AnotherBuildCorner/Hyper_Wheel/Images/RevA1 PCB Pricing.png

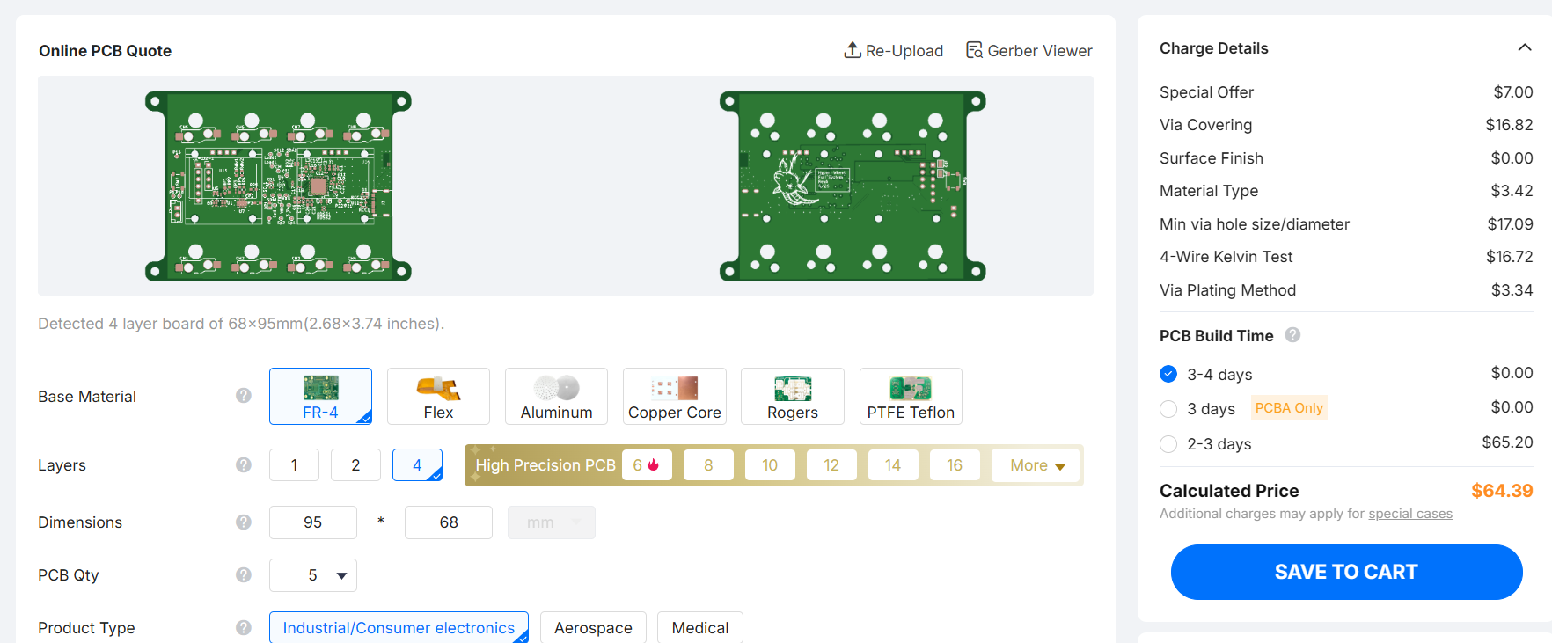
Images/RevA1 PCB Pricing.png
