AnotherBuildCorner/Hyper_Wheel/Ref/Screenshot 2026-04-17 091756.png

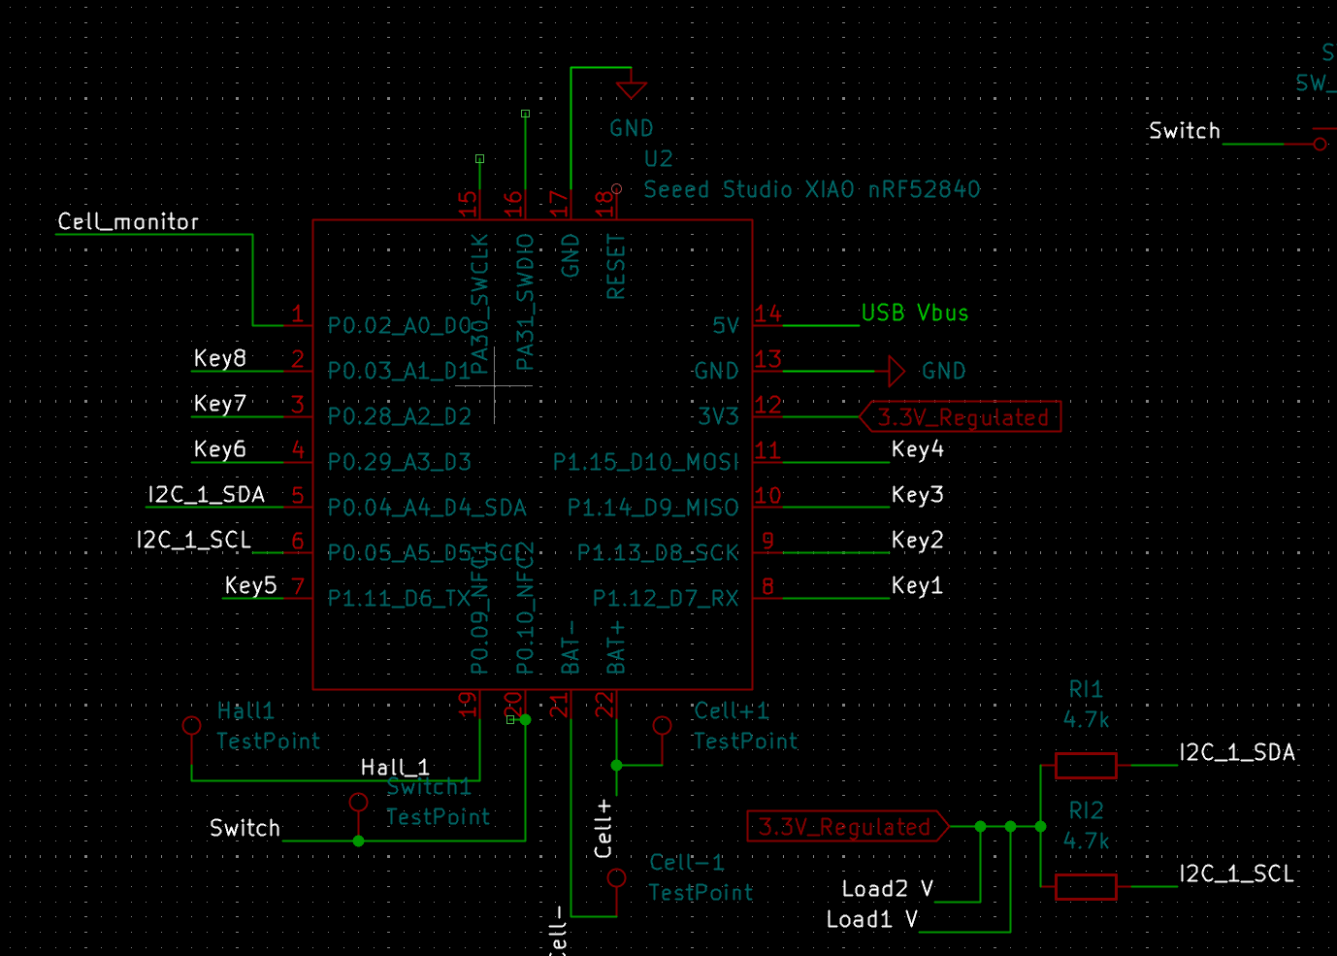
Ref/Screenshot 2026-04-17 091756.png
