AnotherBuildCorner/Hyper_Wheel/PCB/Hyper_Wheel_XIAO/Vendor Parts/marbastlib-main/marbastlib-main/resources/repolist.png

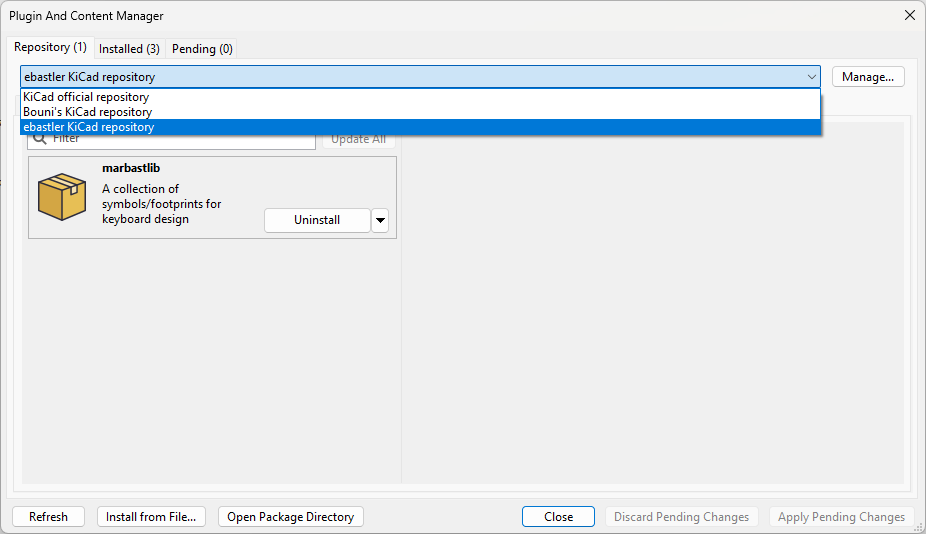
PCB/Hyper_Wheel_XIAO/Vendor Parts/marbastlib-main/marbastlib-main/resources/repolist.png
