AnotherBuildCorner/Hyper_Wheel/PCB/Hyper_Wheel_XIAO/Vendor Parts/marbastlib-main/marbastlib-main/3dmodels/CON_781710004.step

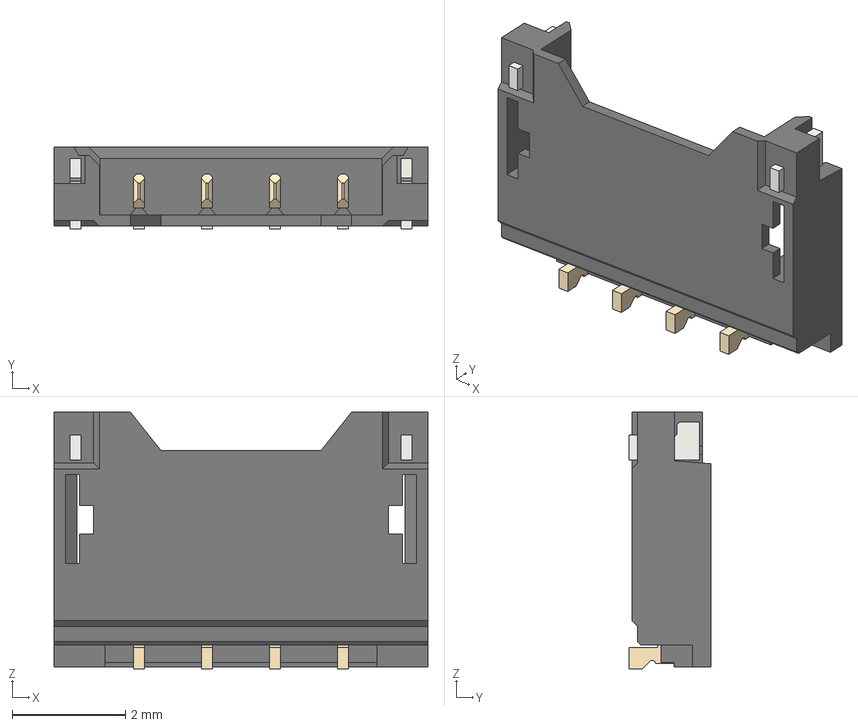
[picture p37: CAD file, 2026-04-03]
PCB/Hyper_Wheel_XIAO/Vendor Parts/marbastlib-main/marbastlib-main/3dmodels/CON_781710004.step
6.60 x 1.45 x 4.53 mm
