AnotherBuildCorner/Hyper_Wheel/PCB/Hyper_Wheel_XIAO/Vendor Parts/marbastlib-main/marbastlib-main/3dmodels/Texas_X2QFN-12_1.6x1.6mm.step

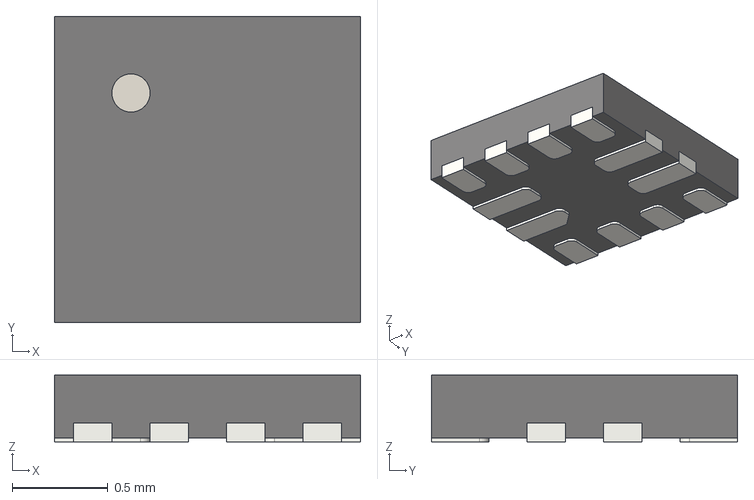
[picture p38: CAD file, 2026-04-03]
PCB/Hyper_Wheel_XIAO/Vendor Parts/marbastlib-main/marbastlib-main/3dmodels/Texas_X2QFN-12_1.6x1.6mm.step
1.60 x 1.60 x 0.35 mm
