AnotherBuildCorner/Hyper_Wheel/PCB/Hyper_Wheel_XIAO/Vendor Parts/marbastlib-main/marbastlib-main/3dmodels/CON_SM13B-SRSS-TB.step

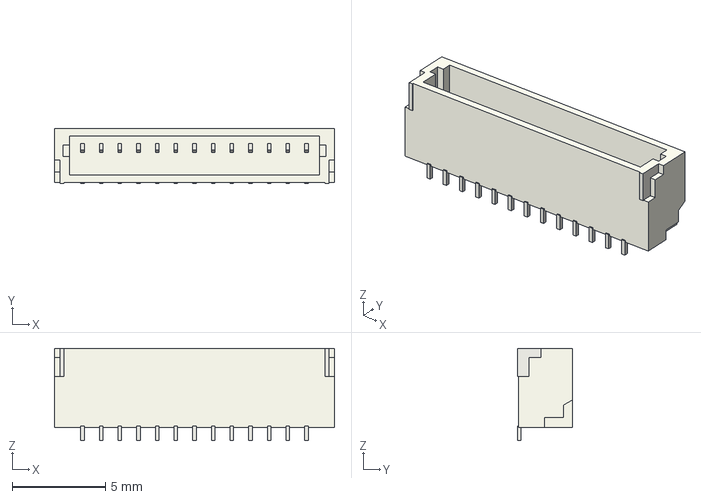
[picture p39: CAD file, 2026-04-03]
PCB/Hyper_Wheel_XIAO/Vendor Parts/marbastlib-main/marbastlib-main/3dmodels/CON_SM13B-SRSS-TB.step
15.0 x 2.96 x 4.95 mm
