AnotherBuildCorner/Hyper_Wheel/PCB/Hyper_Wheel_XIAO/Vendor Parts/marbastlib-main/marbastlib-main/3dmodels/ebyte_E73-2G4M08S1C.step

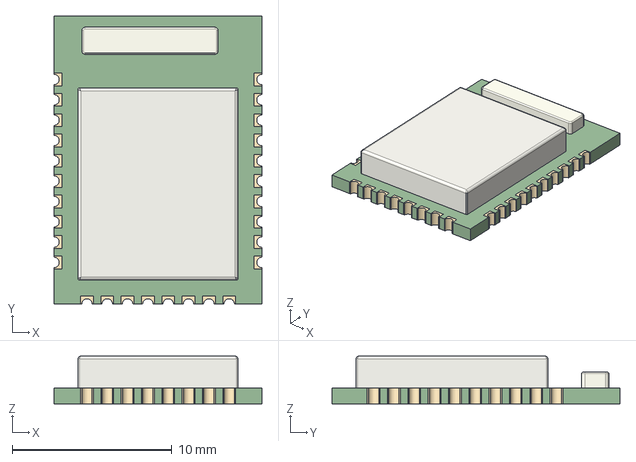
[picture p41: CAD file, 2026-04-03]
PCB/Hyper_Wheel_XIAO/Vendor Parts/marbastlib-main/marbastlib-main/3dmodels/ebyte_E73-2G4M08S1C.step
13.0 x 18.0 x 3.00 mm
