AnotherBuildCorner/Hyper_Wheel/PCB/Hyper_Wheel_XIAO/Vendor Parts/marbastlib-main/marbastlib-main/3dmodels/SpringContact_SameSky_CPG-45-TH-TR.step

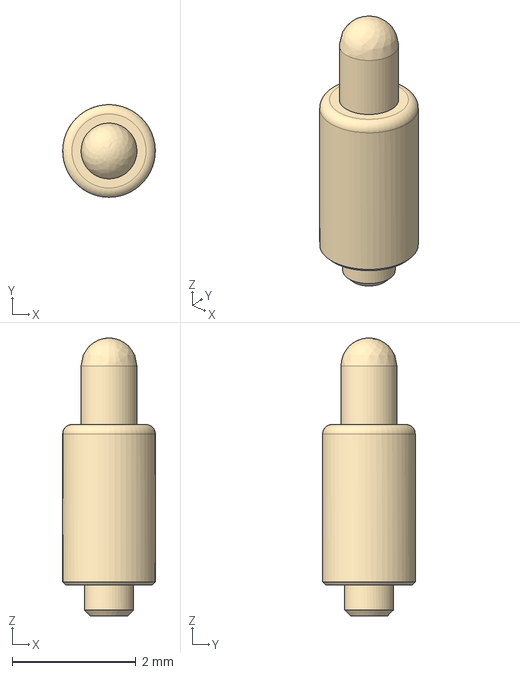
[picture p42: CAD file, 2026-04-03]
PCB/Hyper_Wheel_XIAO/Vendor Parts/marbastlib-main/marbastlib-main/3dmodels/SpringContact_SameSky_CPG-45-TH-TR.step
1.50 x 1.50 x 4.50 mm
