AnotherBuildCorner/Hyper_Wheel/PCB/Hyper_Wheel_XIAO/Vendor Parts/marbastlib-main/marbastlib-main/3dmodels/HS_CPG151101S11_MX.step

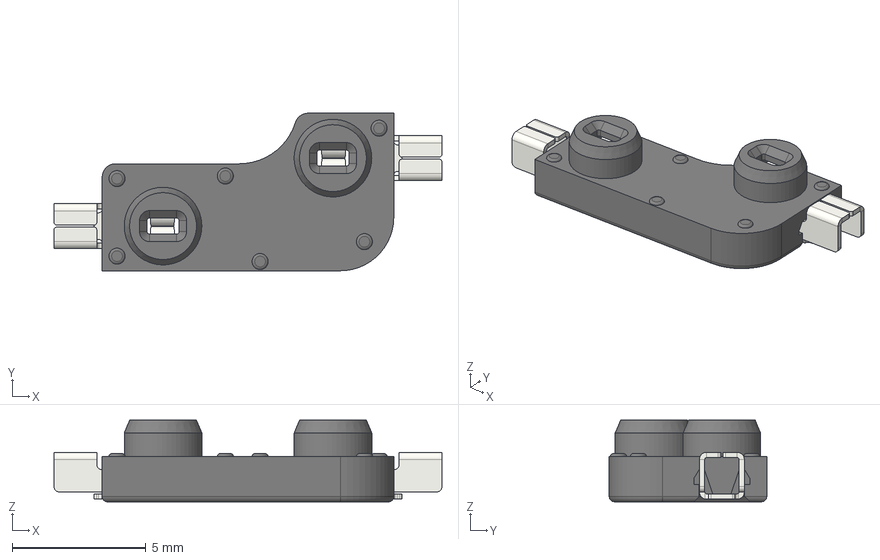
[picture p43: CAD file, 2026-04-03]
PCB/Hyper_Wheel_XIAO/Vendor Parts/marbastlib-main/marbastlib-main/3dmodels/HS_CPG151101S11_MX.step
14.5 x 5.89 x 3.05 mm
Contact x 2
