AnotherBuildCorner/Hyper_Wheel/PCB/Hyper_Wheel_XIAO/Vendor Parts/marbastlib-main/marbastlib-main/3dmodels/SW_SPDT_Alps_SSAJ110100.step

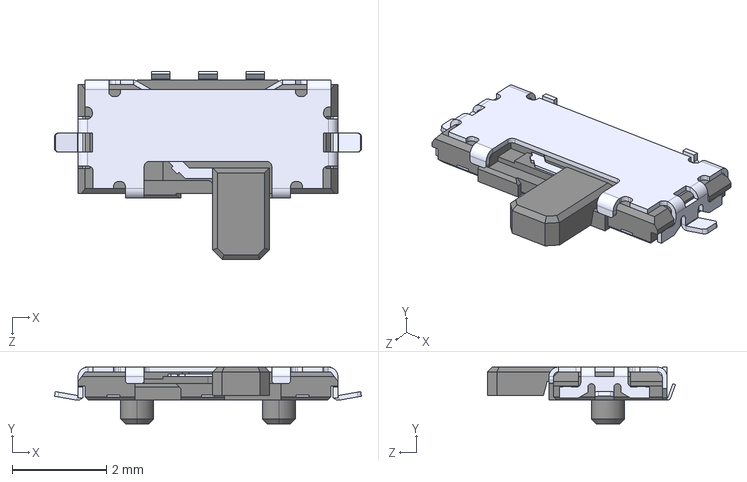
[picture p44: CAD file, 2026-04-03]
PCB/Hyper_Wheel_XIAO/Vendor Parts/marbastlib-main/marbastlib-main/3dmodels/SW_SPDT_Alps_SSAJ110100.step
6.50 x 1.20 x 3.98 mm
