AnotherBuildCorner/Hyper_Wheel/PCB/Hyper_Wheel_XIAO/Vendor Parts/marbastlib-main/marbastlib-main/3dmodels/HS_KS-2P02B01-02_KS33.step

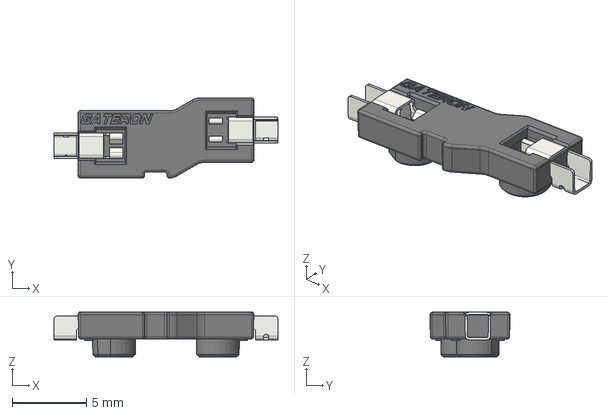
[picture p48: CAD file, 2026-04-03]
PCB/Hyper_Wheel_XIAO/Vendor Parts/marbastlib-main/marbastlib-main/3dmodels/HS_KS-2P02B01-02_KS33.step
15.1 x 5.39 x 3.00 mm
