AnotherBuildCorner/Hyper_Wheel/PCB/Hyper_Wheel_XIAO/Vendor Parts/marbastlib-main/marbastlib-main/3dmodels/SW_Kailh_ULP_CPG1316M_CAP.step

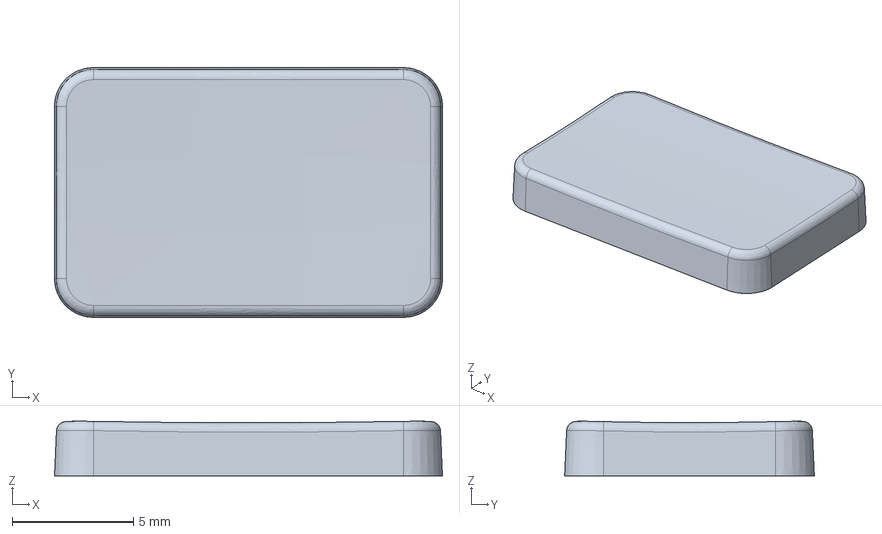
[picture p49: CAD file, 2026-04-03]
PCB/Hyper_Wheel_XIAO/Vendor Parts/marbastlib-main/marbastlib-main/3dmodels/SW_Kailh_ULP_CPG1316M_CAP.step
16.0 x 10.3 x 2.25 mm
