AnotherBuildCorner/Hyper_Wheel/PCB/Hyper_Wheel_XIAO/Vendor Parts/marbastlib-main/marbastlib-main/3dmodels/QFN-14_2x2_Pitch0.4mm.step

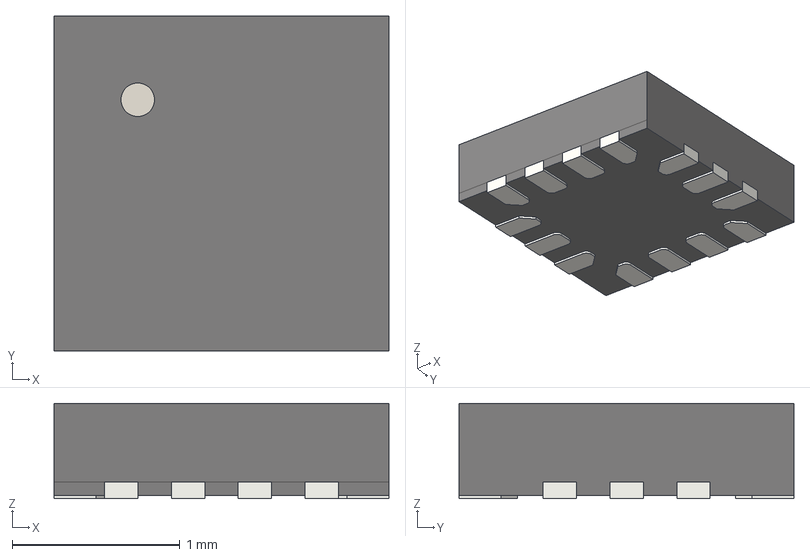
[picture p50: CAD file, 2026-04-03]
PCB/Hyper_Wheel_XIAO/Vendor Parts/marbastlib-main/marbastlib-main/3dmodels/QFN-14_2x2_Pitch0.4mm.step
2.00 x 2.00 x 0.57 mm
