AnotherBuildCorner/Hyper_Wheel/PCB/Hyper_Wheel_XIAO/Vendor Parts/marbastlib-main/marbastlib-main/3dmodels/SW_Kailh_ULP_CPG1316M.step

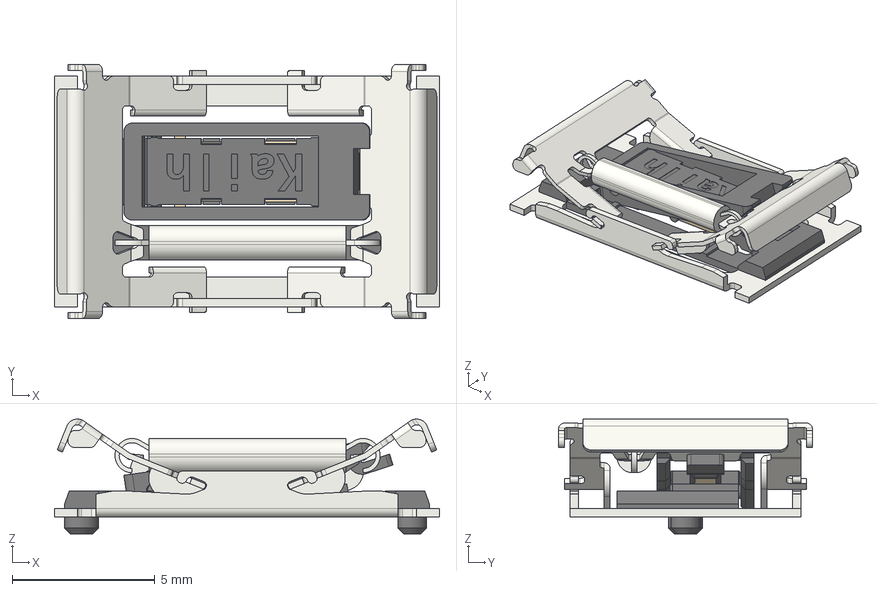
[picture p52: CAD file, 2026-04-03]
PCB/Hyper_Wheel_XIAO/Vendor Parts/marbastlib-main/marbastlib-main/3dmodels/SW_Kailh_ULP_CPG1316M.step
13.5 x 8.90 x 4.03 mm
1316S-»ù×ù¿¨¼þ
PG1316S-»ù×ù
Çý¶¯¸Ë
Æ½ºâ¼Ü-B¼þ
À»É
PG1316S-¶¯½Ó´¥Æ¬-´ ø´¥µã
PG1316S-¾²Æ¬-´ø´¥µ ã
Æ½ºâ¼Ü
