AnotherBuildCorner/Hyper_Wheel/PCB/Hyper_Wheel_XIAO/Vendor Parts/marbastlib-main/marbastlib-main/3dmodels/CON_TYPE-C-31-M-14.step

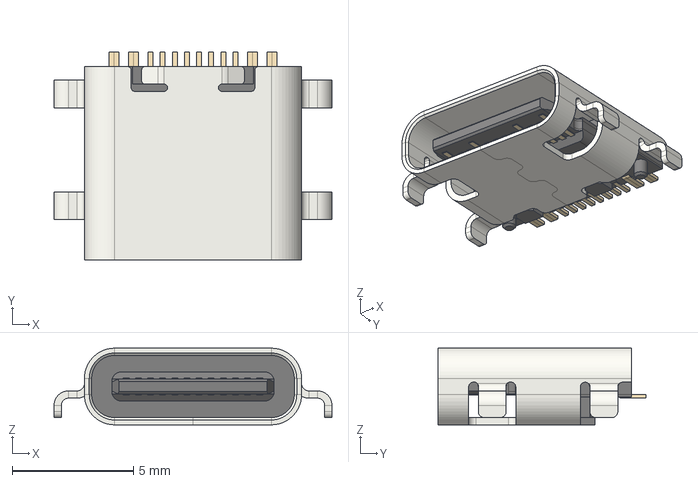
[picture p55: CAD file, 2026-04-03]
PCB/Hyper_Wheel_XIAO/Vendor Parts/marbastlib-main/marbastlib-main/3dmodels/CON_TYPE-C-31-M-14.step
11.5 x 8.56 x 3.16 mm
Shroud
Plastic Body & Connector
