AnotherBuildCorner/Hyper_Wheel/PCB/Hyper_Wheel_XIAO/Vendor Parts/marbastlib-main/marbastlib-main/3dmodels/CON_HC-PBB40C-10DS-0.4V-2.0-02.step

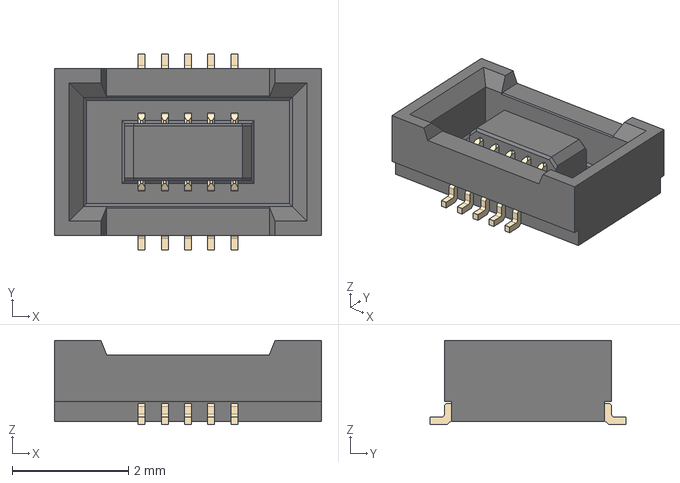
[picture p56: CAD file, 2026-04-03]
PCB/Hyper_Wheel_XIAO/Vendor Parts/marbastlib-main/marbastlib-main/3dmodels/CON_HC-PBB40C-10DS-0.4V-2.0-02.step
4.60 x 3.38 x 1.45 mm
