AnotherBuildCorner/Hyper_Wheel/PCB/Hyper_Wheel_XIAO/Vendor Parts/marbastlib-main/marbastlib-main/3dmodels/Crystal_SMD_2016-4Pin_2.0x1.6mm.step

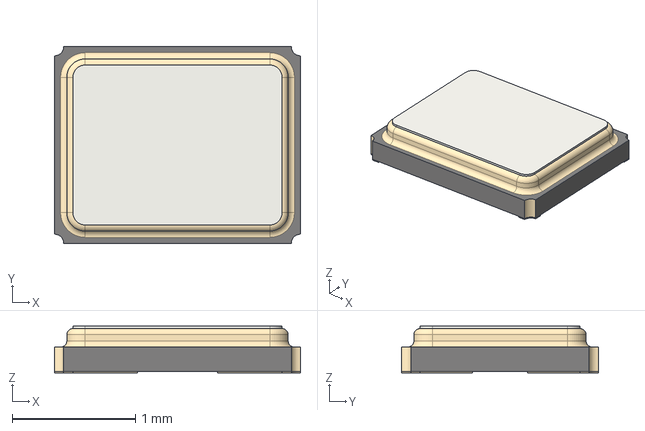
[picture p65: CAD file, 2026-04-03]
PCB/Hyper_Wheel_XIAO/Vendor Parts/marbastlib-main/marbastlib-main/3dmodels/Crystal_SMD_2016-4Pin_2.0x1.6mm.step
2.00 x 1.60 x 0.38 mm
