AnotherBuildCorner/Hyper_Wheel/PCB/Hyper_Wheel_XIAO/Vendor Parts/marbastlib-main/marbastlib-main/3dmodels/CON_XUNPU_FPC-0.5AL-20PB.step

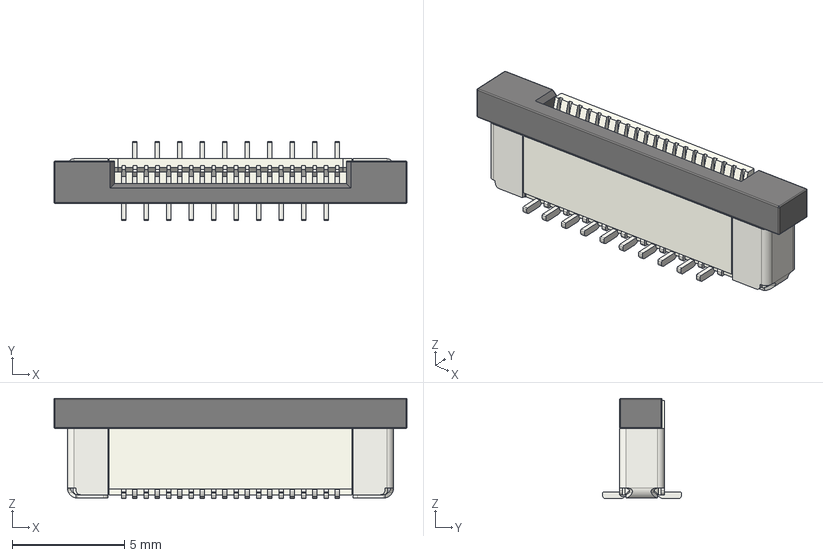
[picture p66: CAD file, 2026-04-03]
PCB/Hyper_Wheel_XIAO/Vendor Parts/marbastlib-main/marbastlib-main/3dmodels/CON_XUNPU_FPC-0.5AL-20PB.step
15.7 x 3.52 x 4.47 mm
