AnotherBuildCorner/Hyper_Wheel/PCB/Hyper_Wheel_XIAO/Vendor Parts/marbastlib-main/marbastlib-main/3dmodels/RP2040-Matrix.step

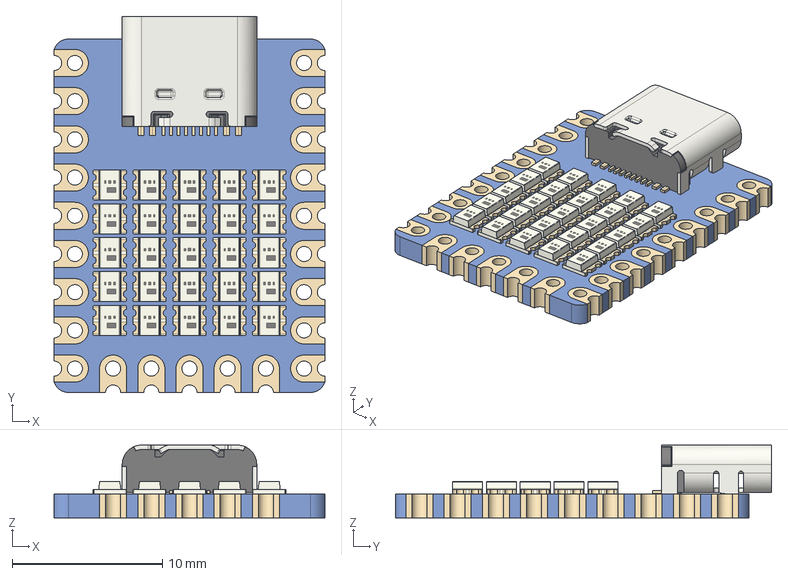
[picture p69: CAD file, 2026-04-03]
PCB/Hyper_Wheel_XIAO/Vendor Parts/marbastlib-main/marbastlib-main/3dmodels/RP2040-Matrix.step
18.0 x 25.0 x 4.85 mm
LED_WS2812_2020 x 25
ConPins
PcbPins
Mold
Frame
