AnotherBuildCorner/Hyper_Wheel/PCB/Hyper_Wheel_XIAO/Vendor Parts/marbastlib-main/marbastlib-main/3dmodels/ROT_SKYLOONG_HS.step

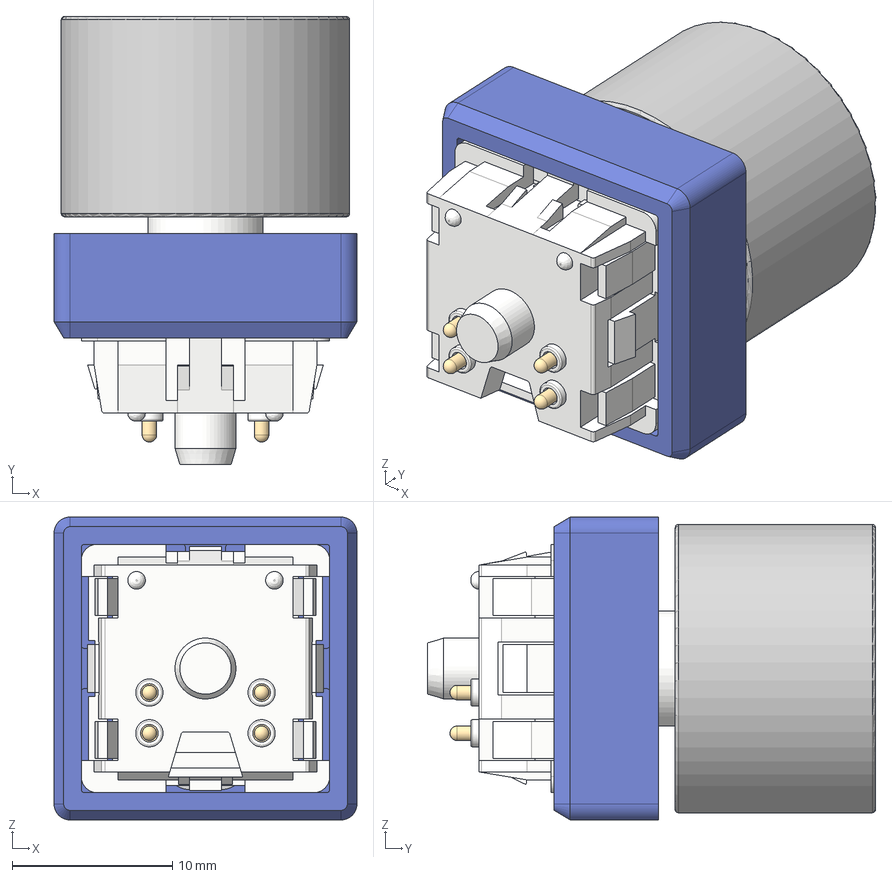
[picture p72: CAD file, 2026-04-03]
PCB/Hyper_Wheel_XIAO/Vendor Parts/marbastlib-main/marbastlib-main/3dmodels/ROT_SKYLOONG_HS.step
18.9 x 27.9 x 18.9 mm
Top
Shaft
Pogo Pin x 4
Bottom
Top_1
Cover
Knob
