AnotherBuildCorner/Hyper_Wheel/PCB/Hyper_Wheel_XIAO/Vendor Parts/marbastlib-main/marbastlib-main/3dmodels/ANT_Johanson_2450AT18D0100001E v1.step

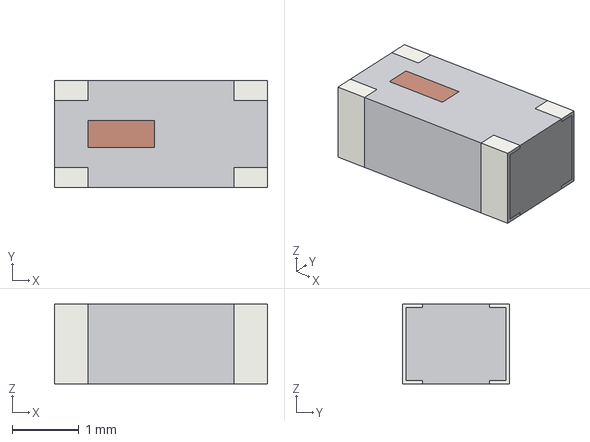
[picture p75: CAD file, 2026-04-03]
PCB/Hyper_Wheel_XIAO/Vendor Parts/marbastlib-main/marbastlib-main/3dmodels/ANT_Johanson_2450AT18D0100001E v1.step
3.20 x 1.60 x 1.20 mm
