AnotherBuildCorner/Hyper_Wheel/PCB/Hyper_Wheel_XIAO/Vendor Parts/marbastlib-main/marbastlib-main/3dmodels/L_Bourns_SRP6050CA.step

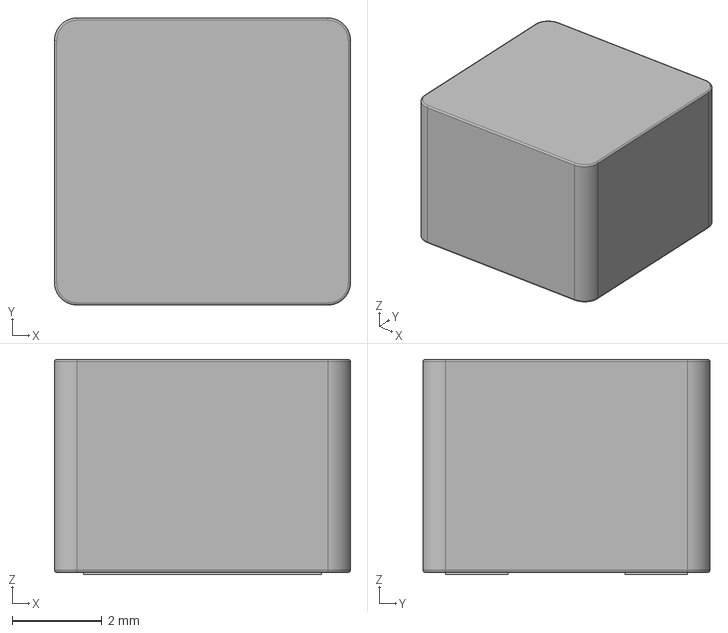
[picture p76: CAD file, 2026-04-03]
PCB/Hyper_Wheel_XIAO/Vendor Parts/marbastlib-main/marbastlib-main/3dmodels/L_Bourns_SRP6050CA.step
6.60 x 6.40 x 4.80 mm
