AnotherBuildCorner/Hyper_Wheel/PCB/Hyper_Wheel_XIAO/Vendor Parts/marbastlib-main/marbastlib-main/3dmodels/Crystal_SMD_2012-2Pin_2.0x1.2mm.step

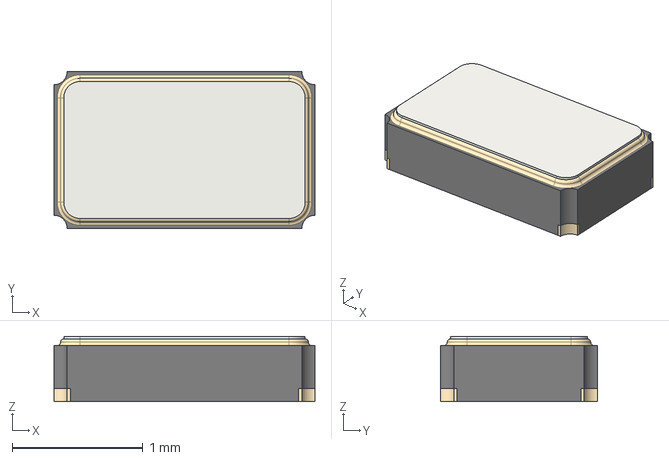
[picture p77: CAD file, 2026-04-03]
PCB/Hyper_Wheel_XIAO/Vendor Parts/marbastlib-main/marbastlib-main/3dmodels/Crystal_SMD_2012-2Pin_2.0x1.2mm.step
2.00 x 1.20 x 0.5 mm
