AnotherBuildCorner/Hyper_Wheel/PCB/Hyper_Wheel_XIAO/Vendor Parts/marbastlib-main/marbastlib-main/3dmodels/CON_XUNPU_FPC-05F-16PH20.step

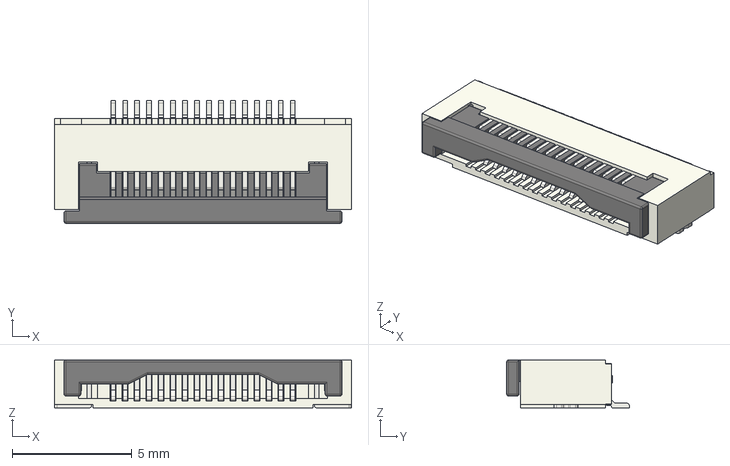
[picture p78: CAD file, 2026-04-03]
PCB/Hyper_Wheel_XIAO/Vendor Parts/marbastlib-main/marbastlib-main/3dmodels/CON_XUNPU_FPC-05F-16PH20.step
12.4 x 5.12 x 2.00 mm
