AnotherBuildCorner/Hyper_Wheel/PCB/Hyper_Wheel_XIAO/Vendor Parts/marbastlib-main/marbastlib-main/3dmodels/USB_C_Receptacle_GCT_USB4510-03-1-A.step

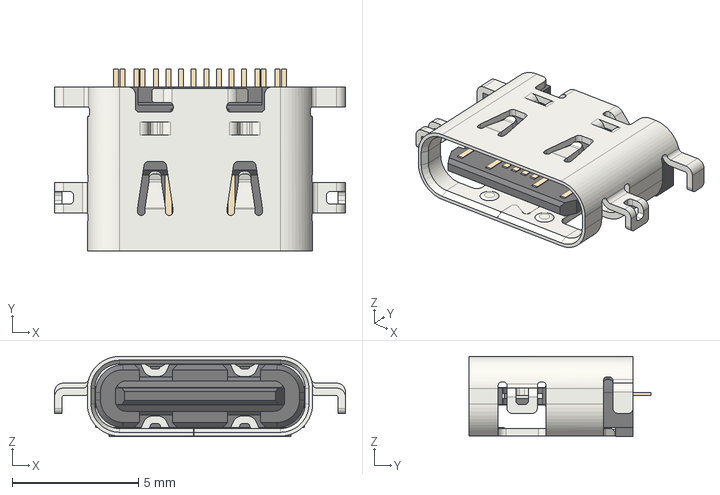
[picture p79: CAD file, 2026-04-03]
PCB/Hyper_Wheel_XIAO/Vendor Parts/marbastlib-main/marbastlib-main/3dmodels/USB_C_Receptacle_GCT_USB4510-03-1-A.step
11.5 x 7.20 x 3.18 mm
