AnotherBuildCorner/Hyper_Wheel/PCB/Hyper_Wheel_XIAO/Vendor Parts/marbastlib-main/marbastlib-main/3dmodels/seeeduino_xiao_rp2040.step

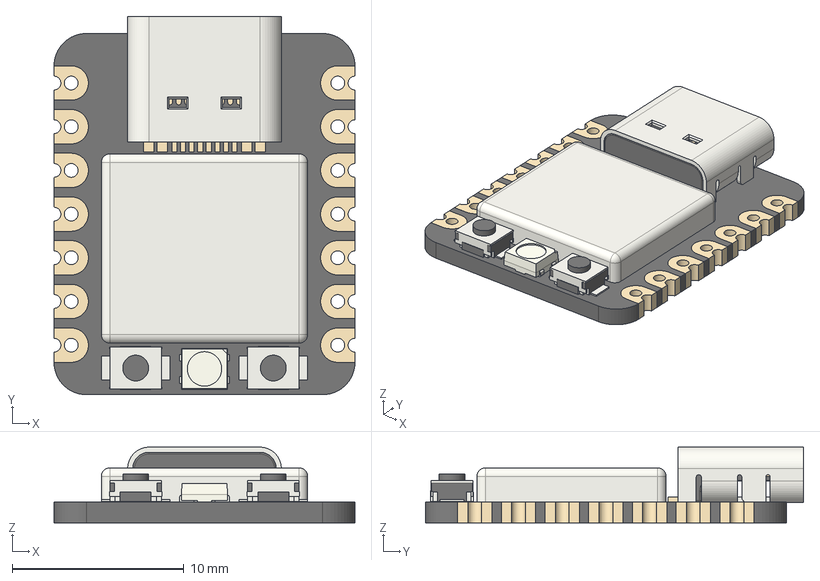
[picture p81: CAD file, 2026-04-03]
PCB/Hyper_Wheel_XIAO/Vendor Parts/marbastlib-main/marbastlib-main/3dmodels/seeeduino_xiao_rp2040.step
17.5 x 22.0 x 4.40 mm
type-c v2
smd_button v3
DOUT
DIN
VSS
VDD
smd_button v3(Mirror)
