AnotherBuildCorner/Hyper_Wheel/PCB/Hyper_Wheel_XIAO/Vendor Parts/marbastlib-main/marbastlib-main/3dmodels/CON_TYPE-C-31-M-12.step

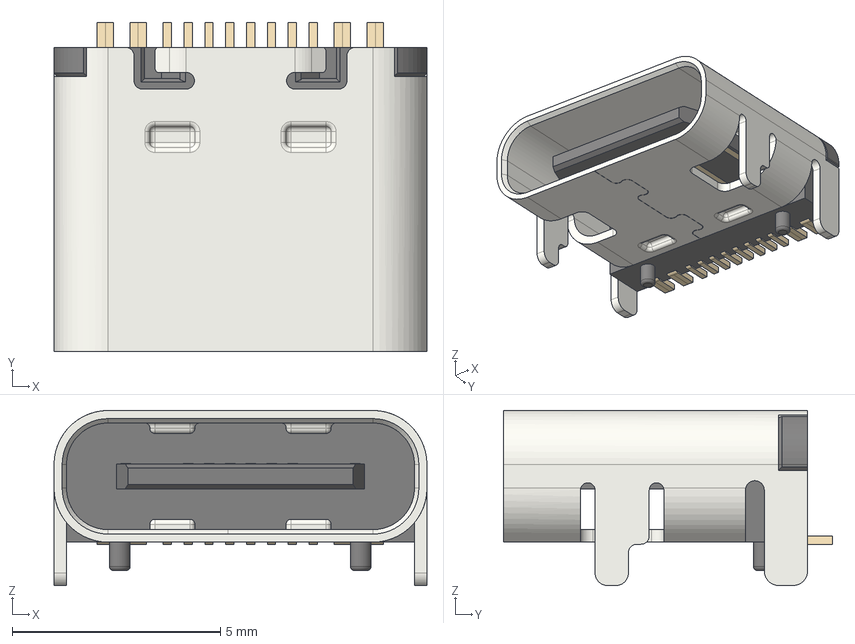
[picture p82: CAD file, 2026-04-03]
PCB/Hyper_Wheel_XIAO/Vendor Parts/marbastlib-main/marbastlib-main/3dmodels/CON_TYPE-C-31-M-12.step
8.95 x 7.90 x 4.20 mm
ConPins
PcbPins
Mold
Frame
