AnotherBuildCorner/Hyper_Wheel/PCB/Hyper_Wheel_XIAO/Vendor Parts/marbastlib-main/marbastlib-main/3dmodels/HS_CPG135001S30_Choc.step

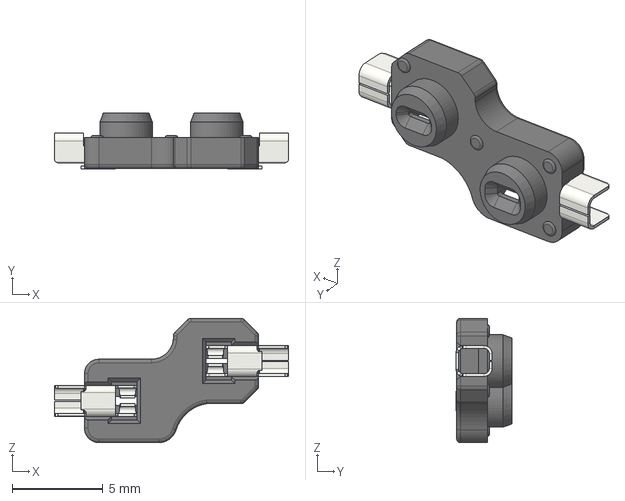
[picture p83: CAD file, 2026-04-03]
PCB/Hyper_Wheel_XIAO/Vendor Parts/marbastlib-main/marbastlib-main/3dmodels/HS_CPG135001S30_Choc.step
12.9 x 3.09 x 6.85 mm
pin x 2
socket
