AnotherBuildCorner/Hyper_Wheel/PCB/Hyper_Wheel_XIAO/Vendor Parts/marbastlib-main/marbastlib-main/3dmodels/SW_Kailh_CPG1316S-2_CAP.step

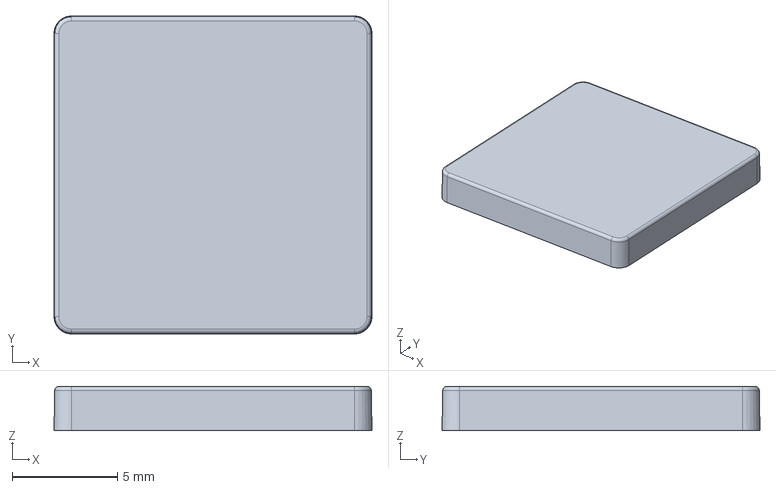
[picture p87: CAD file, 2026-04-03]
PCB/Hyper_Wheel_XIAO/Vendor Parts/marbastlib-main/marbastlib-main/3dmodels/SW_Kailh_CPG1316S-2_CAP.step
15.1 x 15.1 x 2.10 mm
