AnotherBuildCorner/Hyper_Wheel/PCB/Hyper_Wheel_XIAO/Vendor Parts/marbastlib-main/marbastlib-main/3dmodels/Diodes_UDFN1212-3_Type-C.step

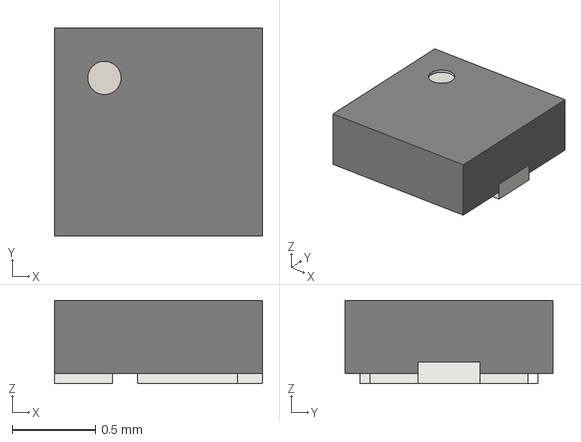
[picture p88: CAD file, 2026-04-03]
PCB/Hyper_Wheel_XIAO/Vendor Parts/marbastlib-main/marbastlib-main/3dmodels/Diodes_UDFN1212-3_Type-C.step
1.25 x 1.25 x 0.5 mm
