AnotherBuildCorner/Hyper_Wheel/PCB/Hyper_Wheel_XIAO/Vendor Parts/marbastlib-main/marbastlib-main/3dmodels/Mounting_Wuerth_WA-SMSI-M2.5_H1mm_9774010151R.step

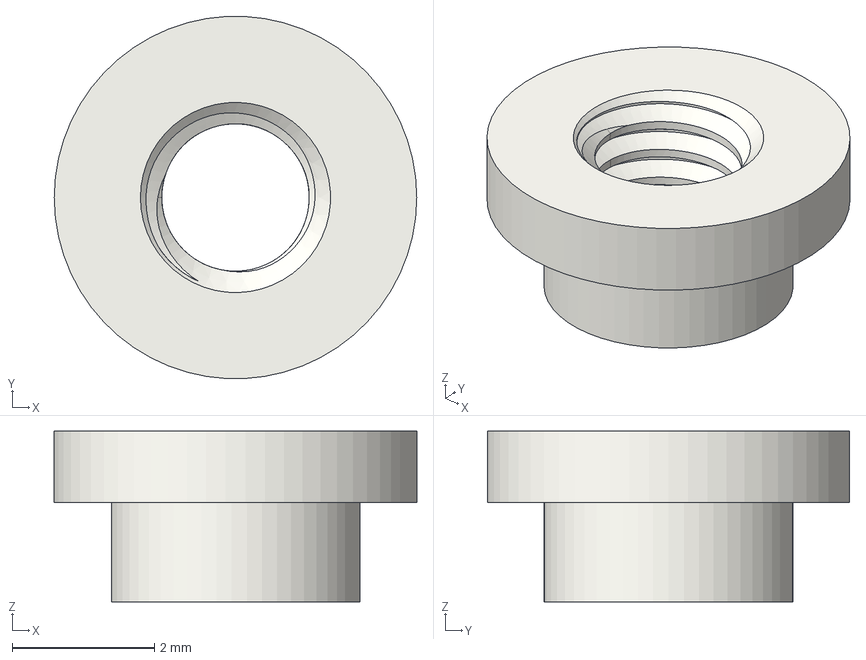
[picture p92: CAD file, 2026-04-03]
PCB/Hyper_Wheel_XIAO/Vendor Parts/marbastlib-main/marbastlib-main/3dmodels/Mounting_Wuerth_WA-SMSI-M2.5_H1mm_9774010151R.step
5.10 x 5.09 x 2.40 mm
