AnotherBuildCorner/Hyper_Wheel/PCB/Hyper_Wheel_XIAO/Vendor Parts/marbastlib-main/marbastlib-main/3dmodels/Speaker_SELTECH_CR1511L025YN8WP.step

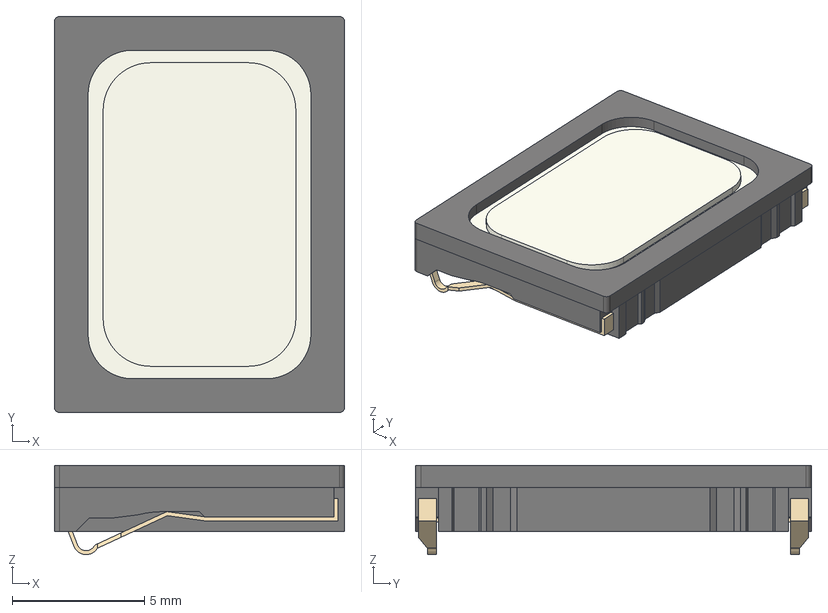
[picture p94: CAD file, 2026-04-03]
PCB/Hyper_Wheel_XIAO/Vendor Parts/marbastlib-main/marbastlib-main/3dmodels/Speaker_SELTECH_CR1511L025YN8WP.step
11.0 x 15.0 x 3.38 mm
