AnotherBuildCorner/Hyper_Wheel/PCB/Hyper_Wheel_XIAO/Vendor Parts/marbastlib-main/marbastlib-main/3dmodels/CON_HytePro_M411P_Receptacle_1x04.step

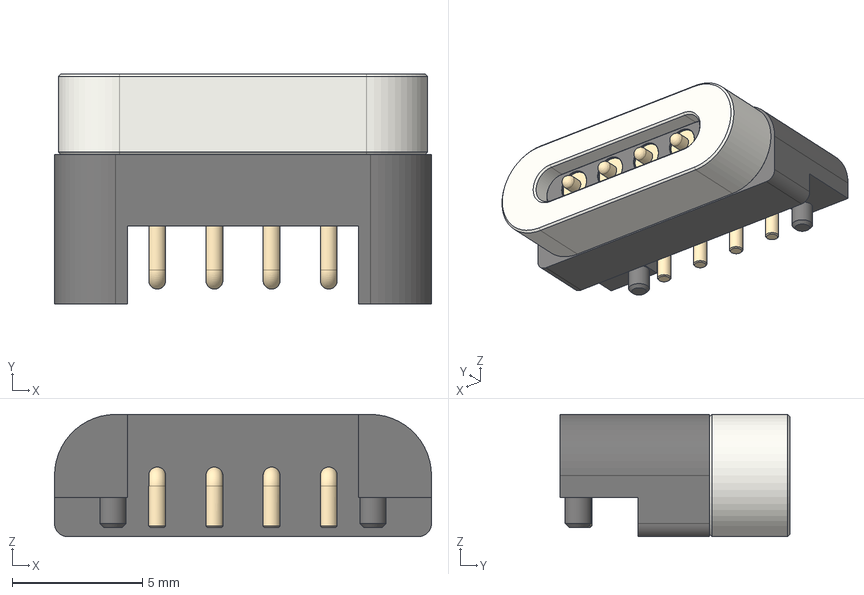
[picture p96: CAD file, 2026-04-03]
PCB/Hyper_Wheel_XIAO/Vendor Parts/marbastlib-main/marbastlib-main/3dmodels/CON_HytePro_M411P_Receptacle_1x04.step
14.5 x 8.85 x 4.70 mm
Magnetic Connector Female - MiddlePart
Magnetic Connector Female-tip_Standard
Magnetic Connector Female v2 - MountingPart
