AnotherBuildCorner/Hyper_Wheel/PCB/Hyper_Wheel_XIAO/Vendor Parts/marbastlib-main/marbastlib-main/3dmodels/Texas_RYK0018A_WQFN-HR-18.step

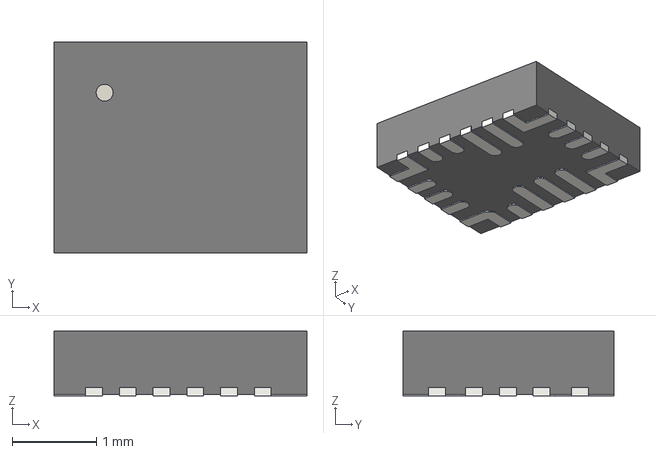
[picture p97: CAD file, 2026-04-03]
PCB/Hyper_Wheel_XIAO/Vendor Parts/marbastlib-main/marbastlib-main/3dmodels/Texas_RYK0018A_WQFN-HR-18.step
3.00 x 2.50 x 0.77 mm
