AnotherBuildCorner/Hyper_Wheel/PCB/Hyper_Wheel_XIAO/Vendor Parts/marbastlib-main/marbastlib-main/3dmodels/CON_HC-PBB40C-10DP-0.4V-02.step

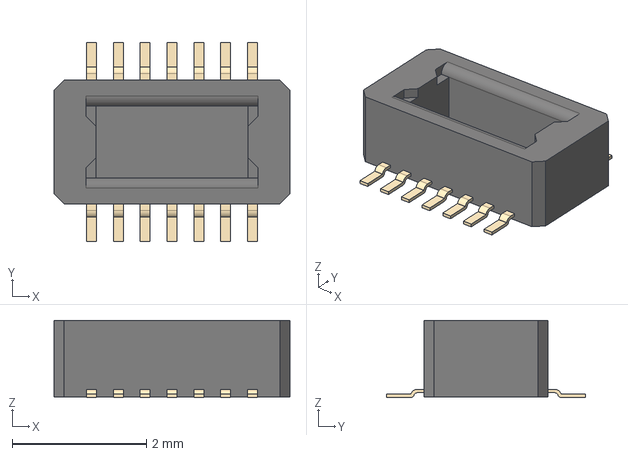
[picture p98: CAD file, 2026-04-03]
PCB/Hyper_Wheel_XIAO/Vendor Parts/marbastlib-main/marbastlib-main/3dmodels/CON_HC-PBB40C-10DP-0.4V-02.step
3.52 x 2.97 x 1.15 mm
