AnotherBuildCorner/Hyper_Wheel/PCB/Hyper_Wheel_XIAO/Vendor Parts/marbastlib-main/marbastlib-main/3dmodels/CON_HytePro_M411P_Plug_1x04.step

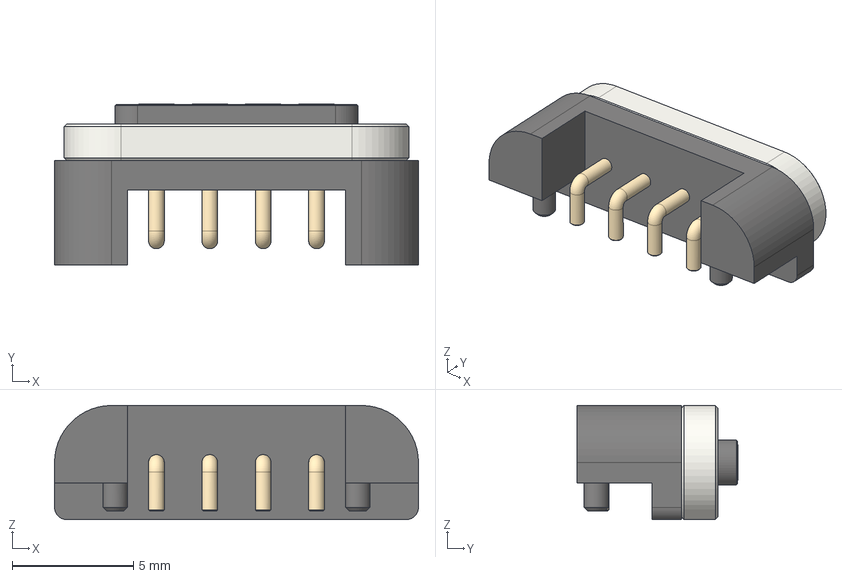
[picture p100: CAD file, 2026-04-03]
PCB/Hyper_Wheel_XIAO/Vendor Parts/marbastlib-main/marbastlib-main/3dmodels/CON_HytePro_M411P_Plug_1x04.step
15.0 x 6.64 x 4.70 mm
Magnetic Connector Male - MiddlePart
Magnetic Connector Male - MountingPart
Magnetic Connector Male-tip_Standard
