AnotherBuildCorner/Hyper_Wheel/PCB/Hyper_Wheel_XIAO/Vendor Parts/marbastlib-main/marbastlib-main/3dmodels/CON_HC-PBB40C-10DS-0.4V-4.0-02.step

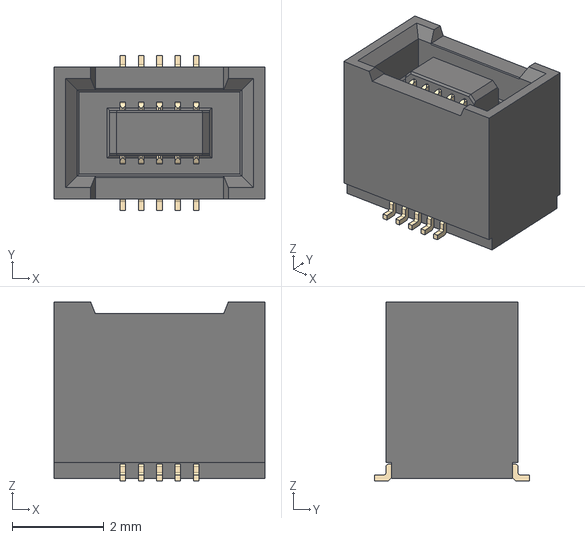
[picture p104: CAD file, 2026-04-03]
PCB/Hyper_Wheel_XIAO/Vendor Parts/marbastlib-main/marbastlib-main/3dmodels/CON_HC-PBB40C-10DS-0.4V-4.0-02.step
4.60 x 3.38 x 3.90 mm
