AnotherBuildCorner/Hyper_Wheel/PCB/Hyper_Wheel_XIAO/Vendor Parts/marbastlib-main/marbastlib-main/3dmodels/Texas_DSBGA-9_1.62x1.58mm_Layout3x3_P0.5mm.step

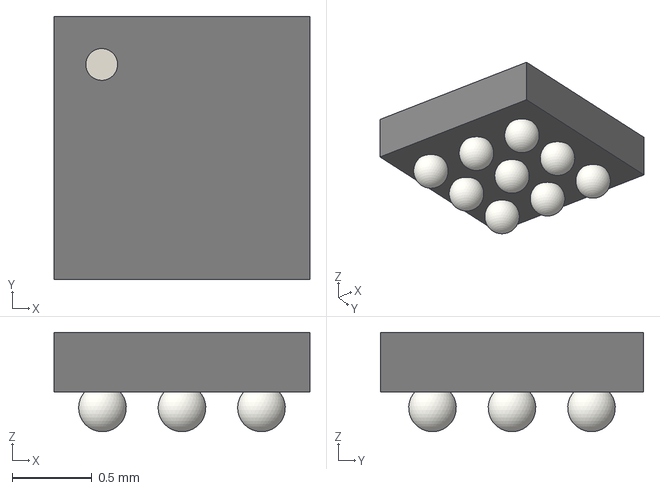
[picture p108: CAD file, 2026-04-03]
PCB/Hyper_Wheel_XIAO/Vendor Parts/marbastlib-main/marbastlib-main/3dmodels/Texas_DSBGA-9_1.62x1.58mm_Layout3x3_P0.5mm.step
1.61 x 1.65 x 0.625 mm
