AnotherBuildCorner/Hyper_Wheel/PCB/Hyper_Wheel_XIAO/Vendor Parts/marbastlib-main/marbastlib-main/3dmodels/USB_C_Receptacle_GCT_USB4505-03-0-A.step

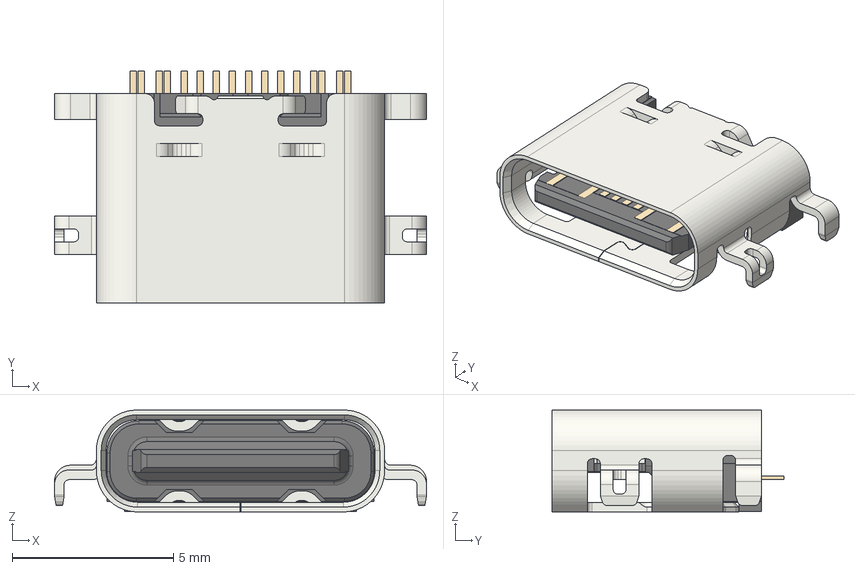
[picture p109: CAD file, 2026-04-03]
PCB/Hyper_Wheel_XIAO/Vendor Parts/marbastlib-main/marbastlib-main/3dmodels/USB_C_Receptacle_GCT_USB4505-03-0-A.step
11.5 x 7.20 x 3.16 mm
USB4505-03-0-A_PART1
USB4505-03-0-A_PART2
