AnotherBuildCorner/Hyper_Wheel/PCB/Hyper_Wheel_XIAO/Vendor Parts/marbastlib-main/marbastlib-main/3dmodels/HS_KS-2P02B01-01_MX.step

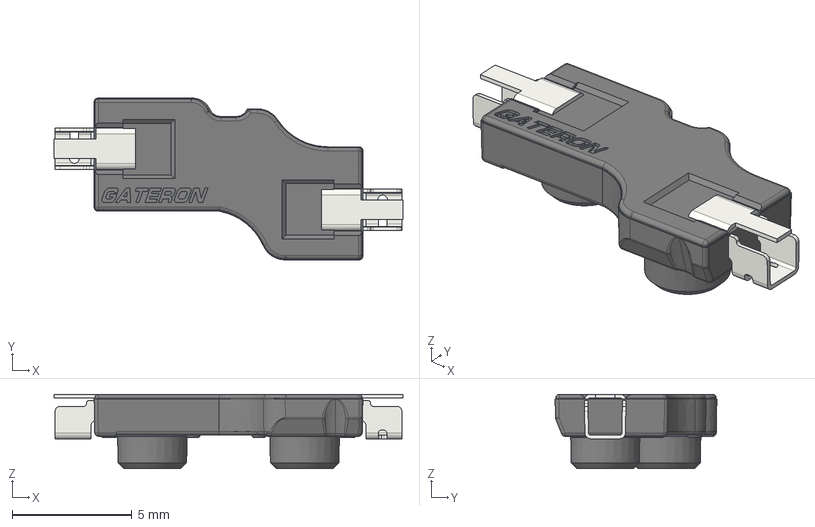
[picture p112: CAD file, 2026-04-03]
PCB/Hyper_Wheel_XIAO/Vendor Parts/marbastlib-main/marbastlib-main/3dmodels/HS_KS-2P02B01-01_MX.step
14.6 x 6.74 x 3.10 mm
