AnotherBuildCorner/Hyper_Wheel/PCB/Hyper_Wheel_XIAO/Vendor Parts/marbastlib-main/marbastlib-main/3dmodels/QFN-13_3x4mm_P0.5mm.step

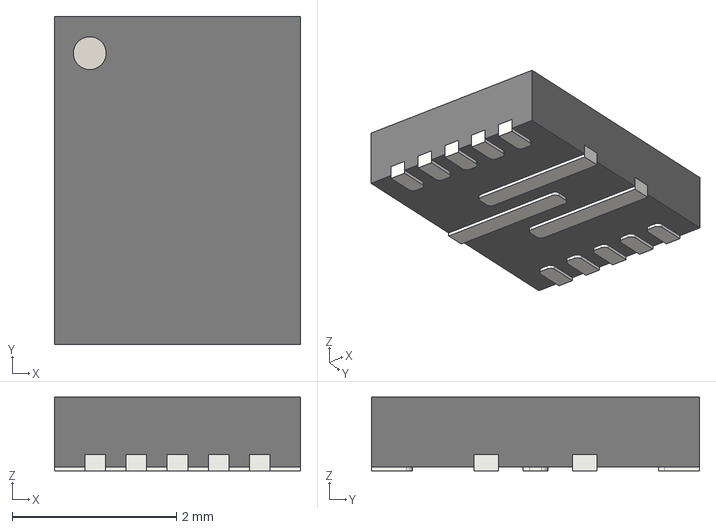
[picture p114: CAD file, 2026-04-03]
PCB/Hyper_Wheel_XIAO/Vendor Parts/marbastlib-main/marbastlib-main/3dmodels/QFN-13_3x4mm_P0.5mm.step
3.00 x 4.00 x 0.9 mm
