AnotherBuildCorner/Hyper_Wheel/Firmware/Hyper_Wheel Firmware 1.0/src/action_layer.cpp

#include "action_layer.h"

#include <Arduino.h>
#include <string.h>

#include "encoder.h"
#include "interface.h"

namespace {

constexpr uint32_t SYSTEM_BUTTON_HOLD_MS = 500;
constexpr uint16_t PRESET_PICKER_STEPS_PER_ITEM = 16;
constexpr EncoderId MAIN_ENCODER = ENCODER_A;
constexpr uint8_t MAIN_ENCODER_CONFIG_INDEX = 0;

uint8_t clampProfileIndex(const KeymapConfig* config, uint8_t index) {
    if (config == nullptr || config->profileCount == 0) {
        return 0;
    }

    if (index >= config->profileCount) {
        return 0;
    }

    return index;
}

void applyProfileEncoderFeel(ActionLayerState& state) {
    if (state.config == nullptr || state.config->profileCount == 0) {
        return;
    }

    uint8_t active = clampProfileIndex(state.config, state.config->activeProfile);
    encoderSetStepCounts(
    MAIN_ENCODER,
    state.config->profiles[active].encoders[MAIN_ENCODER_CONFIG_INDEX].stepsPerDetent
);
}

void applyPresetPickerEncoderFeel() {
    encoderSetStepCounts(MAIN_ENCODER, PRESET_PICKER_STEPS_PER_ITEM);
}

void applyActivePreset(ActionLayerState& state, uint8_t newPreset) {
    if (state.config == nullptr || state.deviceState == nullptr) {
        return;
    }

    if (state.config->profileCount == 0) {
        return;
    }

    newPreset = clampProfileIndex(state.config, newPreset);
    uint8_t current = clampProfileIndex(state.config, state.config->activeProfile);

    if (newPreset != current) {
        state.deviceState->previousPreset = current;
    }

    state.deviceState->activePreset = newPreset;
    state.config->activeProfile = newPreset;

    applyProfileEncoderFeel(state);

    Serial.print("[PRESET] active=");
    Serial.print(newPreset);
    Serial.print(" previous=");
    Serial.println(state.deviceState->previousPreset);
}

void togglePreviousPreset(ActionLayerState& state) {
    if (state.config == nullptr || state.deviceState == nullptr) {
        return;
    }

    if (state.config->profileCount < 2) {
        return;
    }

    uint8_t current = clampProfileIndex(state.config, state.config->activeProfile);
    uint8_t previous = clampProfileIndex(state.config, state.deviceState->previousPreset);

    if (previous == current) {
        previous = (current == 0) ? 1 : 0;
    }

    applyActivePreset(state, previous);
}

void enterPresetPicker(ActionLayerState& state) {
    if (state.config == nullptr || state.config->profileCount == 0) {
        return;
    }

    state.mode = MODE_PRESET_PICKER;
    state.highlightedPreset = clampProfileIndex(state.config, state.config->activeProfile);
    applyPresetPickerEncoderFeel();

    Serial.print("[PICKER] open highlight=");
    Serial.println(state.highlightedPreset);
}

void exitToNormal(ActionLayerState& state) {
    state.mode = MODE_NORMAL;
    state.systemHoldHandled = false;
    state.systemButtonPressMs = 0;
    applyProfileEncoderFeel(state);

    Serial.println("[PICKER] exit");
}

bool updateSystemButtonModeTransitions(ActionLayerState& state) {
    bool uiChanged = false;

    if (wasSystemButtonPressed()) {
        state.systemButtonPressMs = millis();
        state.systemHoldHandled = false;
    }

    if (isSystemButtonDown() &&
        !state.systemHoldHandled &&
        state.mode == MODE_NORMAL) {

        uint32_t heldMs = millis() - state.systemButtonPressMs;
        if (heldMs >= SYSTEM_BUTTON_HOLD_MS) {
            state.systemHoldHandled = true;
            state.suppressNextPickerRelease = true;
            enterPresetPicker(state);
            uiChanged = true;
        }
    }

    if (wasSystemButtonReleased()) {
        if (state.mode == MODE_NORMAL) {
            if (!state.systemHoldHandled) {
                togglePreviousPreset(state);
                uiChanged = true;
            }
        } else if (state.mode == MODE_PRESET_PICKER) {
            if (state.suppressNextPickerRelease) {
                state.suppressNextPickerRelease = false;
            } else {
                applyActivePreset(state, state.highlightedPreset);
                exitToNormal(state);
                uiChanged = true;
            }
        }

        state.systemHoldHandled = false;
        state.systemButtonPressMs = 0;
    }

    return uiChanged;
}

bool handleNormalButtons(ActionLayerState& state) {
    if (state.config == nullptr || state.config->profileCount == 0) {
        return false;
    }

    uint8_t active = clampProfileIndex(state.config, state.config->activeProfile);

    for (uint8_t phys = 0; phys < NUM_BUTTONS; phys++) {
        PhysicalButtonId button = static_cast<PhysicalButtonId>(phys);

        if (!wasButtonPressed(button)) {
            continue;
        }

        LogicalKeySlot logical = physicalToLogical(button, state.orientation);
        const KeyAction& action = state.config->profiles[active].keys[logical];

                Serial.print("[BTN PATH] phys=");
        Serial.print(phys);
        Serial.print(" logical=");
        Serial.print(static_cast<int>(logical));
        Serial.print(" label=");
        Serial.print(action.label);
        Serial.print(" keyid=");
        Serial.println(action.KeyID);

        interfaceSendKeypress(action.KeyID, action.modifiers);
    }

    return false;
}

bool handleNormalEncoder(ActionLayerState& state) {
    if (!encoderHasSteps(MAIN_ENCODER)) {
        return false;
    }

    int8_t steps = getPendingEncoderSteps(MAIN_ENCODER);



    if (state.config == nullptr || state.config->profileCount == 0) {
        return false;
    }

    uint8_t active = clampProfileIndex(state.config, state.config->activeProfile);

    const EncoderBinding& enc =
        state.config->profiles[active].encoders[MAIN_ENCODER_CONFIG_INDEX];

    bool invert = enc.invertDirection;

    while (steps > 0) {
        const KeyAction& action = invert ? enc.counterClockwise : enc.clockwise;
        interfaceSendKeypress(action.KeyID, action.modifiers);
        steps--;

    }

    while (steps < 0) {
        const KeyAction& action = invert ? enc.clockwise : enc.counterClockwise;
        interfaceSendKeypress(action.KeyID, action.modifiers);
        steps++;

    }

    return false;
}
bool handleNormalMode(ActionLayerState& state) {
    bool uiChanged = false;
    uiChanged |= handleNormalButtons(state);
    uiChanged |= handleNormalEncoder(state);
    return uiChanged;
}

bool handlePresetPickerMode(ActionLayerState& state) {
    if (state.config == nullptr || state.config->profileCount == 0) {
        return false;
    }

    bool uiChanged = false;

    if (encoderHasSteps(MAIN_ENCODER)) {
        int8_t steps = getPendingEncoderSteps(MAIN_ENCODER);
        uint8_t before = state.highlightedPreset;

        while (steps > 0) {
            if ((state.highlightedPreset + 1) < state.config->profileCount) {
                state.highlightedPreset++;
            }
            steps--;
        }

        while (steps < 0) {
            if (state.highlightedPreset > 0) {
                state.highlightedPreset--;
            }
            steps++;
        }

        if (state.highlightedPreset != before) {
            Serial.print("[PICKER] highlight=");
            Serial.println(state.highlightedPreset);
            uiChanged = true;
        }
    }

    return uiChanged;
}

const char* getProfileNameSafe(const KeymapConfig* config, uint8_t index) {
    if (config == nullptr || config->profileCount == 0) {
        return "------";
    }

    if (index >= config->profileCount) {
        return "------";
    }

    return config->profiles[index].name;
}

} // namespace

void actionLayerBegin(ActionLayerState& state,
                      KeymapConfig& config,
                      DeviceState& deviceState,
                      OrientationMode orientation) {
    state.mode = MODE_NORMAL;
    state.orientation = orientation;
    state.highlightedPreset = clampProfileIndex(&config, config.activeProfile);
    state.systemButtonPressMs = 0;
    state.systemHoldHandled = false;
    state.config = &config;
    state.deviceState = &deviceState;
    state.suppressNextPickerRelease = false;

    state.deviceState->activePreset = clampProfileIndex(&config, config.activeProfile);
    state.deviceState->previousPreset = clampProfileIndex(&config, deviceState.previousPreset);

    applyProfileEncoderFeel(state);
}

void actionLayerSetOrientation(ActionLayerState& state, OrientationMode orientation) {
    state.orientation = orientation;
}

bool actionLayerUpdate(ActionLayerState& state) {
    bool uiChanged = false;

    buttonsUpdate();
    systemButtonUpdate();
    encoderUpdate();

    uiChanged |= updateSystemButtonModeTransitions(state);

    switch (state.mode) {
        case MODE_PRESET_PICKER:
            uiChanged |= handlePresetPickerMode(state);
            break;

        case MODE_PRESET_EDIT:
            // later
            break;

        case MODE_NORMAL:
        default:
            uiChanged |= handleNormalMode(state);
            break;
    }

    return uiChanged;
}

bool actionLayerInMenu(const ActionLayerState& state) {
    return (state.mode != MODE_NORMAL);
}

const char* actionLayerGetMenuTitle(const ActionLayerState& state) {
    switch (state.mode) {
        case MODE_PRESET_PICKER:
            return "PRESETS";

        case MODE_PRESET_EDIT:
            return "EDIT";

        case MODE_NORMAL:
        default:
            return "NORMAL";
    }
}

const char* actionLayerGetMenuItemLabel(const ActionLayerState& state, uint8_t index) {
    if (state.mode != MODE_PRESET_PICKER || state.config == nullptr) {
        return "------";
    }

    if (index >= 3) {
        return "------";
    }

    uint8_t item = state.highlightedPreset;

    if (index == 0) {
        if (item == 0) {
            return "------";
        }
        return getProfileNameSafe(state.config, item - 1);
    }

    if (index == 1) {
        return getProfileNameSafe(state.config, item);
    }

    if (index == 2) {
        if ((item + 1) >= state.config->profileCount) {
            return "------";
        }
        return getProfileNameSafe(state.config, item + 1);
    }

    return "------";
}
