AnotherBuildCorner/Hyper_Wheel/Firmware/Hyper_Wheel Firmware 1.0/src/buttons.h

#pragma once
#include <stdint.h>
#include "nrf.h"
constexpr uint8_t NUM_BUTTONS = 8;
constexpr uint16_t DEBOUNCE_MS = 20;

constexpr uint8_t PIN_BTN_1 = 7;   // D7,  P1.12
constexpr uint8_t PIN_BTN_2 = 8;   // D8,  P1.13
constexpr uint8_t PIN_BTN_3 = 9;   // D9,  P1.14
constexpr uint8_t PIN_BTN_4 = 10;  // D10, P1.15
constexpr uint8_t PIN_BTN_5 = 6;   // D6,  P1.11
constexpr uint8_t PIN_BTN_6 = 3;   // D3,  P0.29
constexpr uint8_t PIN_BTN_7 = 2;   // D2,  P0.28
constexpr uint8_t PIN_BTN_8 = 1;   // D1,  P0.03

//constexpr uint8_t PUSH_BTN_PIN = 0; // NFC2 P0.10 (borrowed Cell Monitor Pin for testing)
constexpr uint32_t PUSH_BTN_PIN = 31; //PIN_NFC2
constexpr uint32_t HALL_SENSOR_PIN = 30; // NFC1 P0.09 // Move these to Power Handling later.
constexpr uint8_t CELL_MONITOR_PIN = 0; // D0, P0.02

enum PhysicalButtonId : uint8_t {
    PHYS_BTN_1 = 0,
    PHYS_BTN_2,
    PHYS_BTN_3,
    PHYS_BTN_4,
    PHYS_BTN_5,
    PHYS_BTN_6,
    PHYS_BTN_7,
    PHYS_BTN_8
};

enum LogicalKeySlot : uint8_t {
    KEY_TOP_LEFT = 0,
    KEY_TOP_1,
    KEY_TOP_2,
    KEY_TOP_RIGHT,
    KEY_BOTTOM_LEFT,
    KEY_BOTTOM_1,
    KEY_BOTTOM_2,
    KEY_BOTTOM_RIGHT
};

enum OrientationMode : uint8_t {
    ORIENT_0_DEG = 0,
    ORIENT_180_DEG
};
// Maps the physical GPIO to the internal logic layer
LogicalKeySlot physicalToLogical(PhysicalButtonId button, OrientationMode orientation);
// returns the GPIO pin for a given physical button
uint8_t buttonToPin(PhysicalButtonId button);

// launches the button subsystem, call once during setup
void buttonsBegin();
// call periodically from loop to update button states and events
void buttonsUpdate();

// Query functions for button states and events. These will be cleared on the next buttonsUpdate() call.
bool wasButtonPressed(PhysicalButtonId id);
bool wasButtonReleased(PhysicalButtonId id);
bool isButtonDown(PhysicalButtonId id);
void debugPrintButtonPresses(OrientationMode orientation);

//---- System Button
constexpr uint16_t SYSTEM_BUTTON_DEBOUNCE_MS = 20;

void systemButtonBegin();
void systemButtonUpdate();

bool wasSystemButtonPressed();
bool wasSystemButtonReleased();
bool isSystemButtonDown();
