AnotherBuildCorner/Hyper_Wheel/Firmware/Hyper_Wheel Firmware 1.0/src/key_constants.h

#pragma once
#include <stdint.h>
/* ------------- Contains the Universal key ID's used throughout the codebase
 ------------- These are not necessarily the same as USB HID keycodes, 
---------------but they should be consistent across the codebase and can be mapped to USB HID keycodes in usb_hid.cpp */


enum KeyId : uint16_t {
    KEY_NONE = 0,

    KEY_A,
    KEY_B,
    KEY_C,
    KEY_D,
    KEY_E,
    KEY_F,
    KEY_G,
    KEY_H,
    KEY_I,
    KEY_J,
    KEY_K,
    KEY_L,
    KEY_M,
    KEY_N,
    KEY_O,
    KEY_P,
    KEY_Q,
    KEY_R,
    KEY_S,
    KEY_T,
    KEY_U,
    KEY_V,
    KEY_W,
    KEY_X,
    KEY_Y,
    KEY_Z,

    KEY_0,
    KEY_1,
    KEY_2,
    KEY_3,
    KEY_4,
    KEY_5,
    KEY_6,
    KEY_7,
    KEY_8,
    KEY_9,

    KEY_NUMPAD_0,
    KEY_NUMPAD_1,
    KEY_NUMPAD_2,
    KEY_NUMPAD_3,
    KEY_NUMPAD_4,
    KEY_NUMPAD_5,
    KEY_NUMPAD_6,
    KEY_NUMPAD_7,
    KEY_NUMPAD_8,
    KEY_NUMPAD_9,
    KEY_NUMPAD_ENTER,
    KEY_NUMPAD_PLUS,
    KEY_NUMPAD_MINUS,
    KEY_NUMPAD_MULTIPLY,
    KEY_NUMPAD_DIVIDE,
    KEY_NUMPAD_DECIMAL,

    KEY_ENTER,
    KEY_ESC,
    KEY_SPACE,
    KEY_TAB,
    KEY_BACKSPACE,

    KEY_MINUS,
    KEY_EQUAL,
    KEY_LEFT_BRACKET,
    KEY_RIGHT_BRACKET,
    KEY_BACKSLASH,
    KEY_SEMICOLON,
    KEY_APOSTROPHE,
    KEY_GRAVE,
    KEY_COMMA,
    KEY_PERIOD,
    KEY_SLASH,
    KEY_ESCAPE,

    KEY_DELETE,
    KEY_UP,
    KEY_DOWN,
    KEY_LEFT,
    KEY_RIGHT
};

enum ModifierFlags : uint8_t {
    MOD_NONE  = 0,
    MOD_CTRL  = 1 << 0,
    MOD_SHIFT = 1 << 1,
    MOD_ALT   = 1 << 2,
    MOD_GUI   = 1 << 3
};
